mc-b/microSRCP/microSRCP/doc/images/MicroSRCP_Arduino.jpg

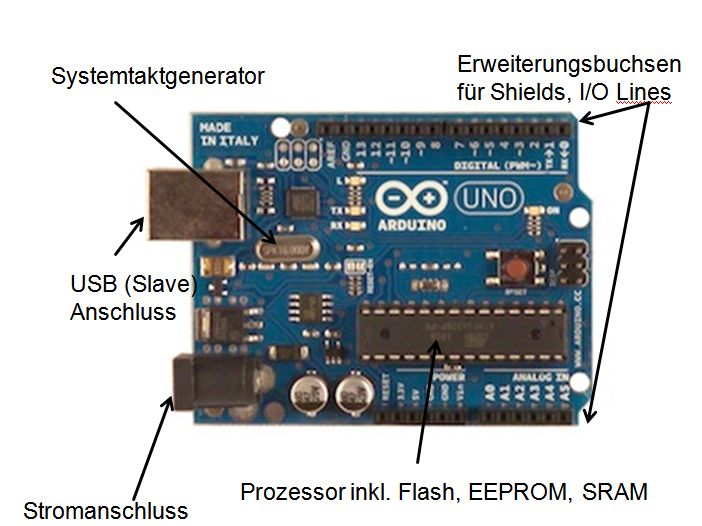
microSRCP/doc/images/MicroSRCP_Arduino.jpg
