mc-b/microSRCP/microSRCP/doc/images/MicroSRCP_ArduinoIDE.jpg

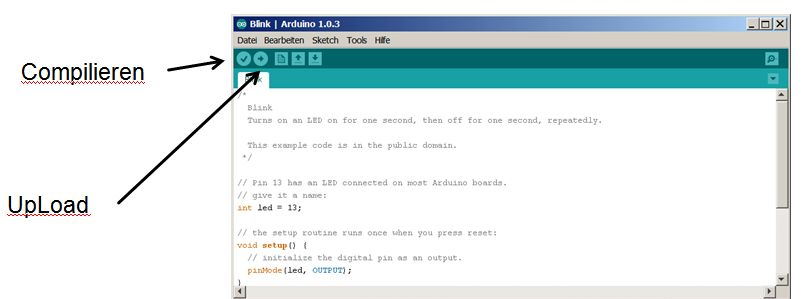
microSRCP/doc/images/MicroSRCP_ArduinoIDE.jpg
