mc-b/microSRCP/microSRCP/doc/images/MicroSRCP_DigitaleZentrale.jpg

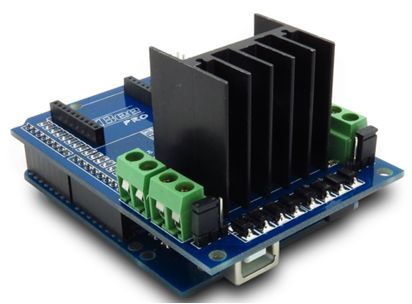
microSRCP/doc/images/MicroSRCP_DigitaleZentrale.jpg
