mc-b/microSRCP/microSRCP/doc/images/MicroSRCP_I2C.JPG

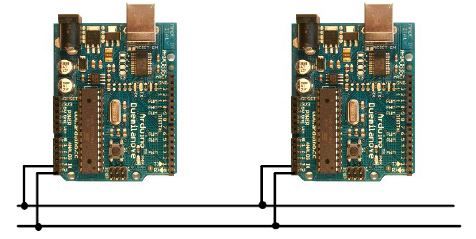
microSRCP/doc/images/MicroSRCP_I2C.JPG
