mc-b/microSRCP/microSRCP/doc/images/MicroSRCP_L293D.jpg

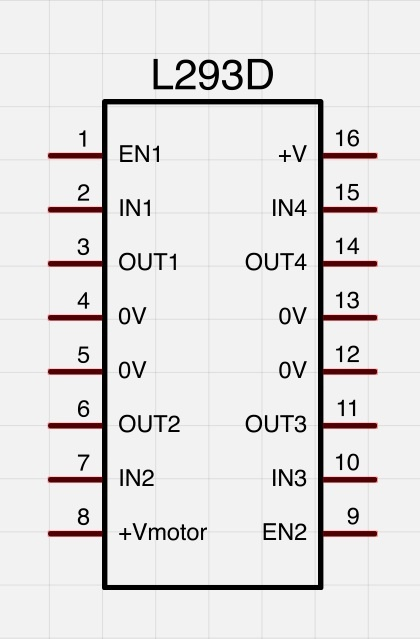
microSRCP/doc/images/MicroSRCP_L293D.jpg
