mc-b/microSRCP/microSRCP/doc/images/MicroSRCP_L298N.png

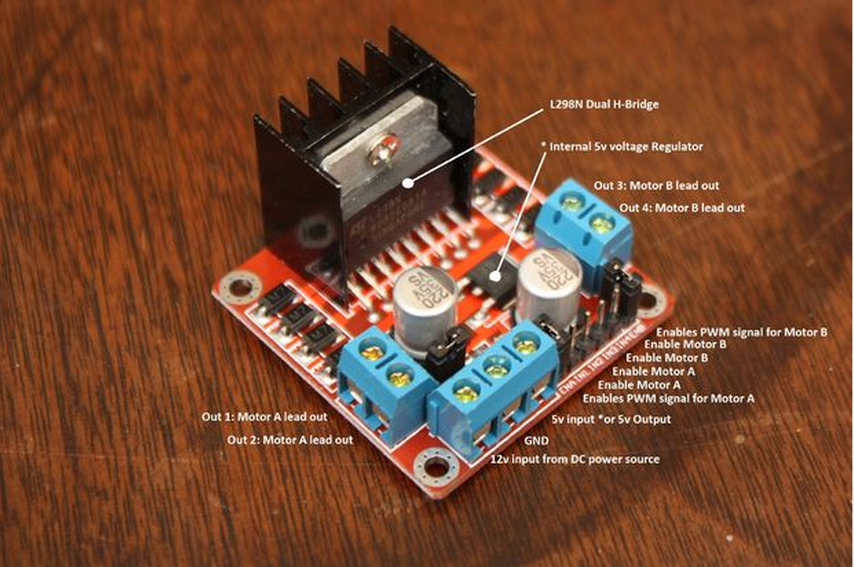
microSRCP/doc/images/MicroSRCP_L298N.png
