mc-b/microSRCP/microSRCP/doc/images/MicroSRCP_Lichtsignal.jpg

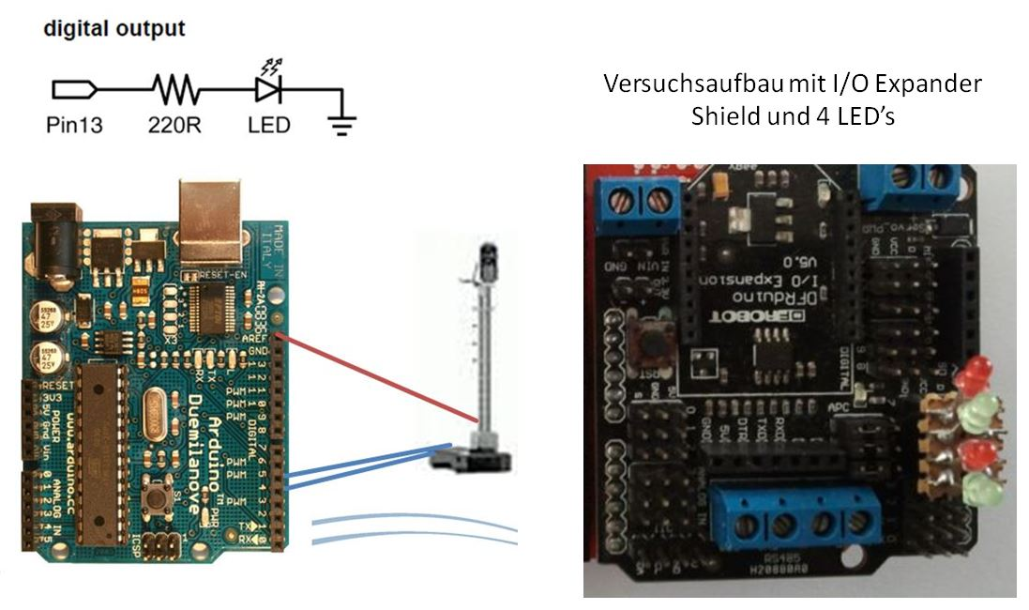
microSRCP/doc/images/MicroSRCP_Lichtsignal.jpg
