mc-b/microSRCP/microSRCP/doc/images/MicroSRCP_Lokomotive.jpg

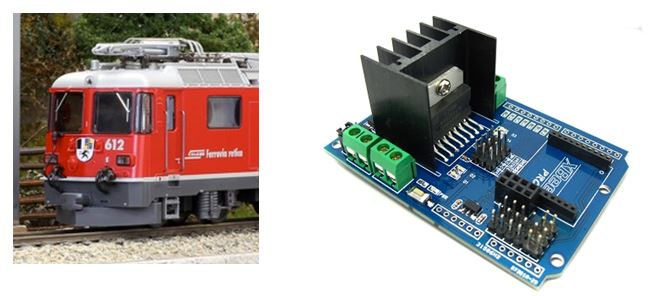
microSRCP/doc/images/MicroSRCP_Lokomotive.jpg
