mc-b/microSRCP/microSRCP/doc/images/MicroSRCP_MotorShield1.jpg

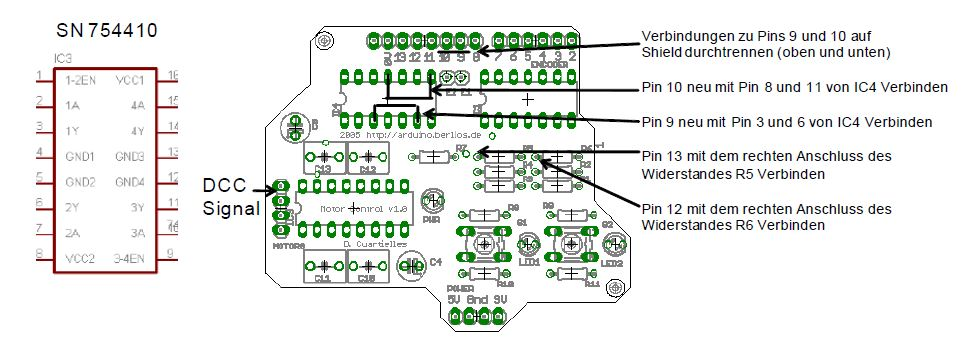
microSRCP/doc/images/MicroSRCP_MotorShield1.jpg
