mc-b/microSRCP/microSRCP/doc/images/MicroSRCP_OpenDCC.jpg

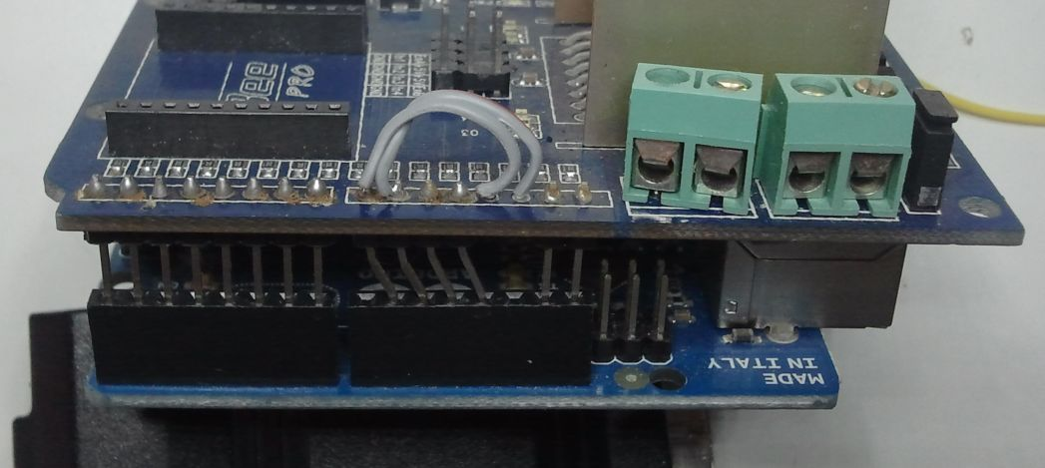
microSRCP/doc/images/MicroSRCP_OpenDCC.jpg
