mc-b/microSRCP/microSRCP/doc/images/MicroSRCP_RocRailZentrale.jpg

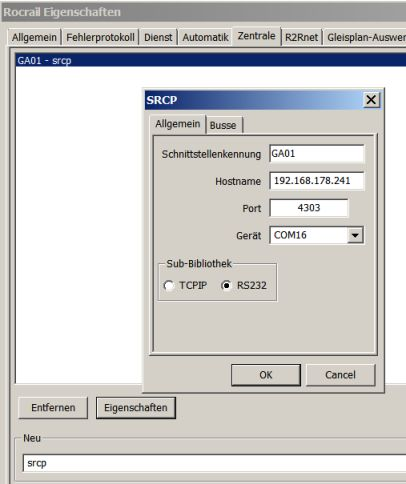
microSRCP/doc/images/MicroSRCP_RocRailZentrale.jpg
