mc-b/microSRCP/microSRCP/doc/images/MicroSRCP_Servo.jpg

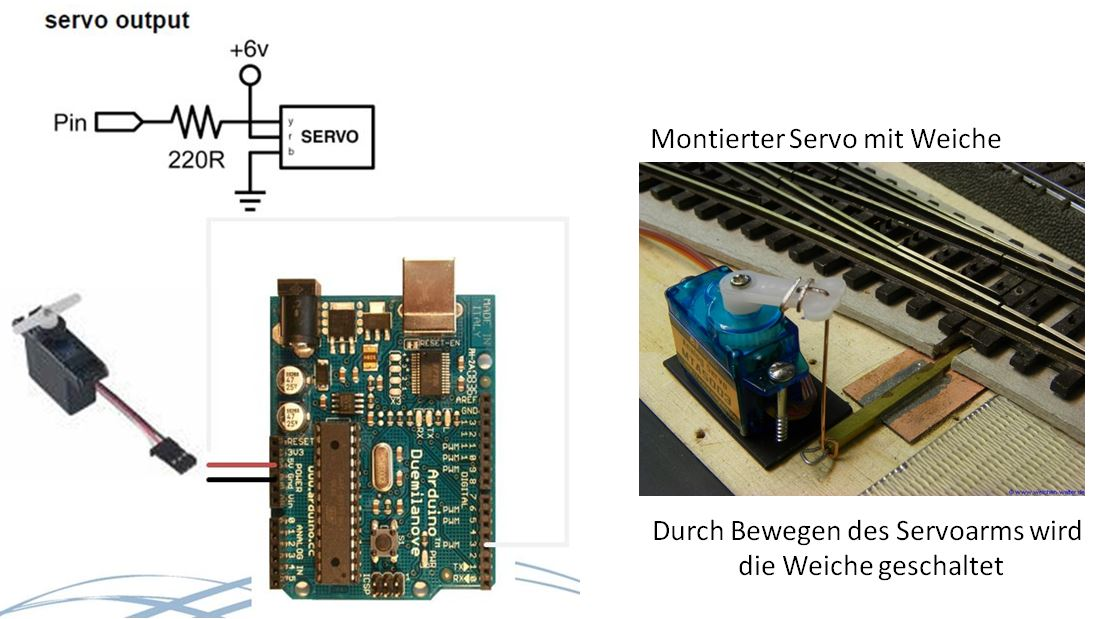
microSRCP/doc/images/MicroSRCP_Servo.jpg
