mc-b/microSRCP/microSRCP/doc/images/MicroSRCP_Shields.jpg

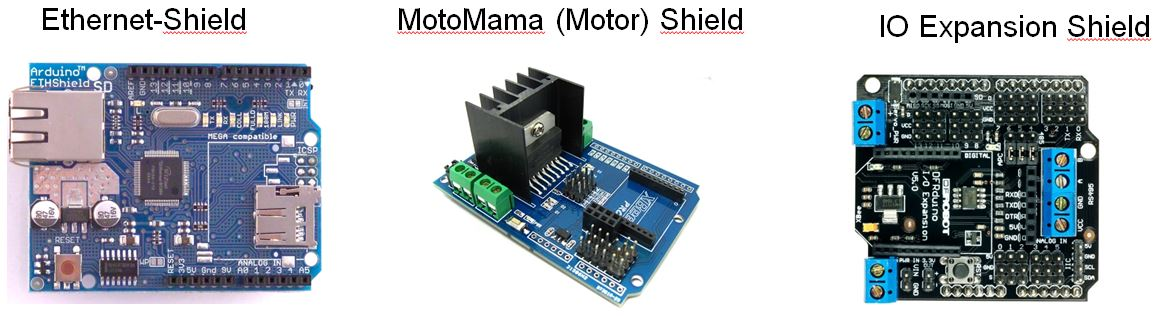
microSRCP/doc/images/MicroSRCP_Shields.jpg
