mc-b/microSRCP/microSRCP/doc/images/MicroSRCP_Steuern.jpg

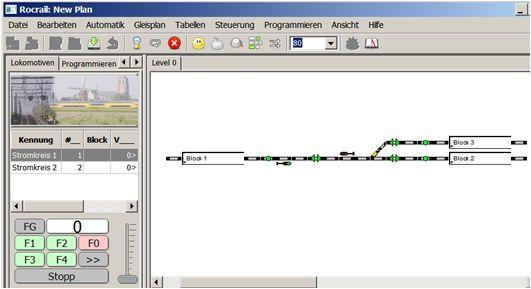
microSRCP/doc/images/MicroSRCP_Steuern.jpg
