mc-b/microSRCP/microSRCP/doc/images/MicroSRCP_Taster.JPG

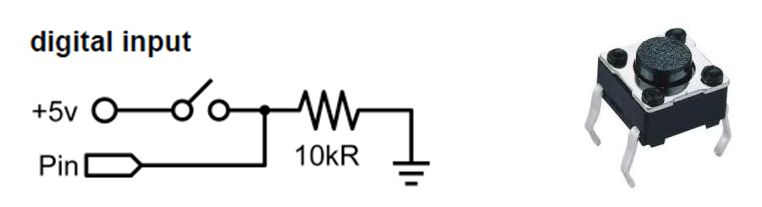
microSRCP/doc/images/MicroSRCP_Taster.JPG
