mc-b/microSRCP/microSRCP/doc/images/MicroSRCP_WaveShield.jpg

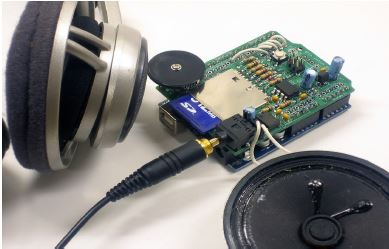
microSRCP/doc/images/MicroSRCP_WaveShield.jpg
